cosimini/cambkb/controllers_code_low_key_count/include/pinout.h

/*
* Define pinout
*/

#define ROW0 15
#define ROW1 14
#define ROW2 16
#define ROW3 10

#define COL0 9
#define COL1 3
#define COL2 4
#define COL3 5
#define COL4 6
#define COL5 7
#define COL6 8

#define EN_PIN 2
